tebl/NoiseMaker/documentation/datasheet/passive_buzzer.png

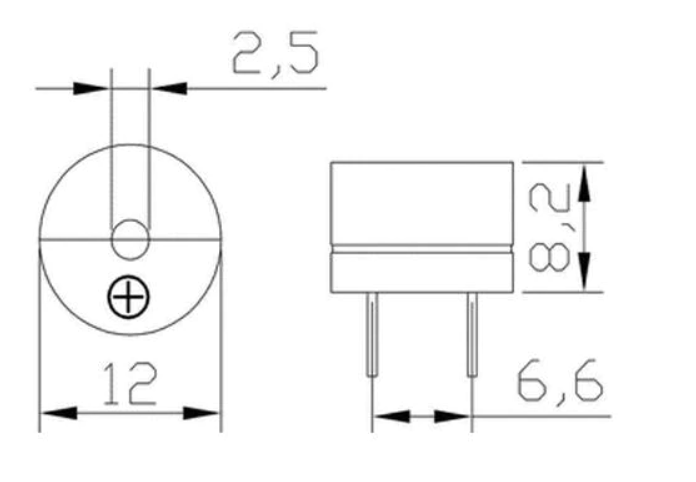
documentation/datasheet/passive_buzzer.png
