tebl/NoiseMaker/gallery/2022-11-01 22.10.24.jpg

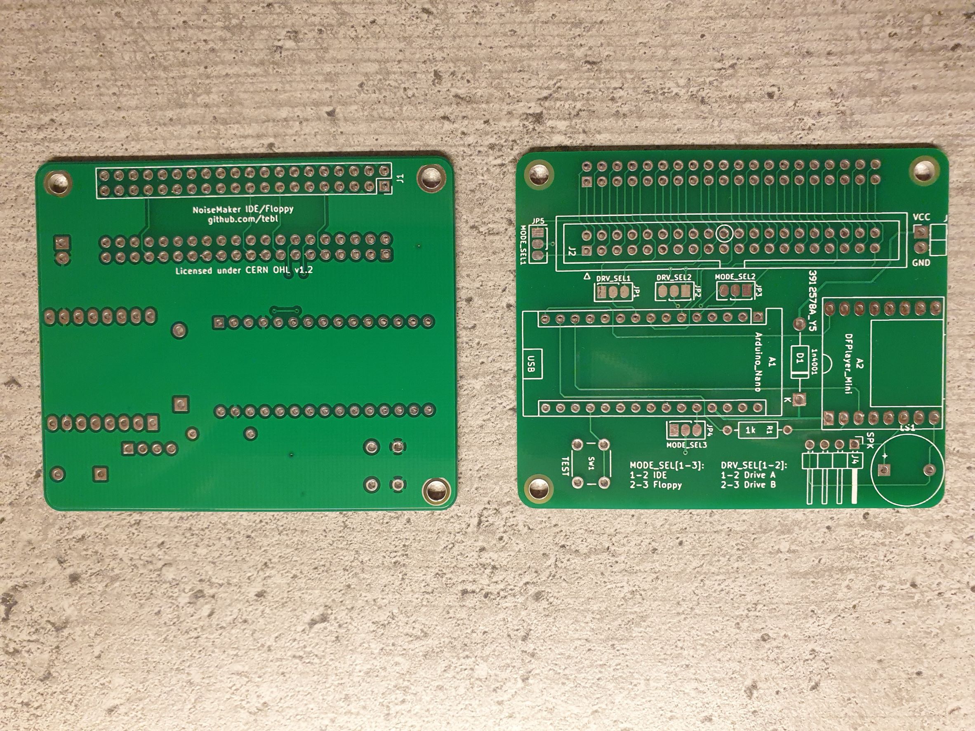
gallery/2022-11-01 22.10.24.jpg
