tebl/NoiseMaker/gallery/2022-11-27 00.52.01.jpg

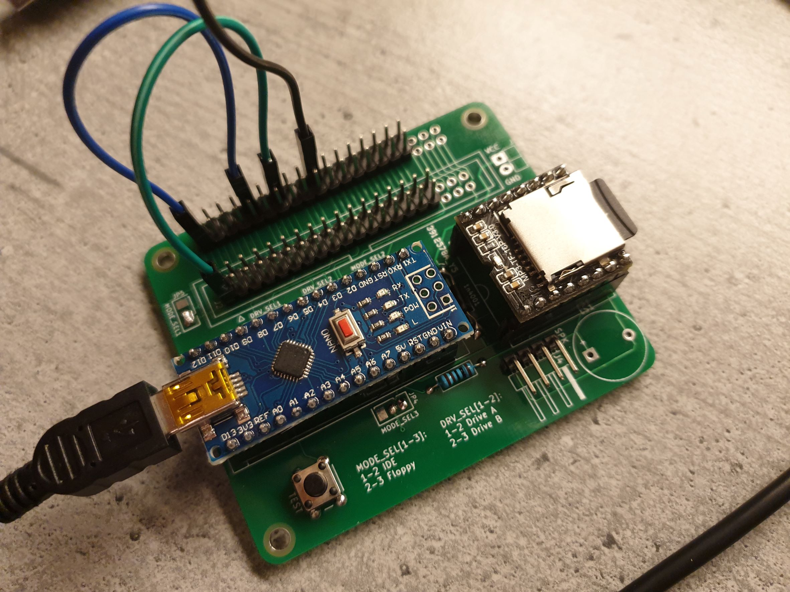
gallery/2022-11-27 00.52.01.jpg
