tebl/NoiseMaker/gallery/2023-01-08 01.55.44.jpg

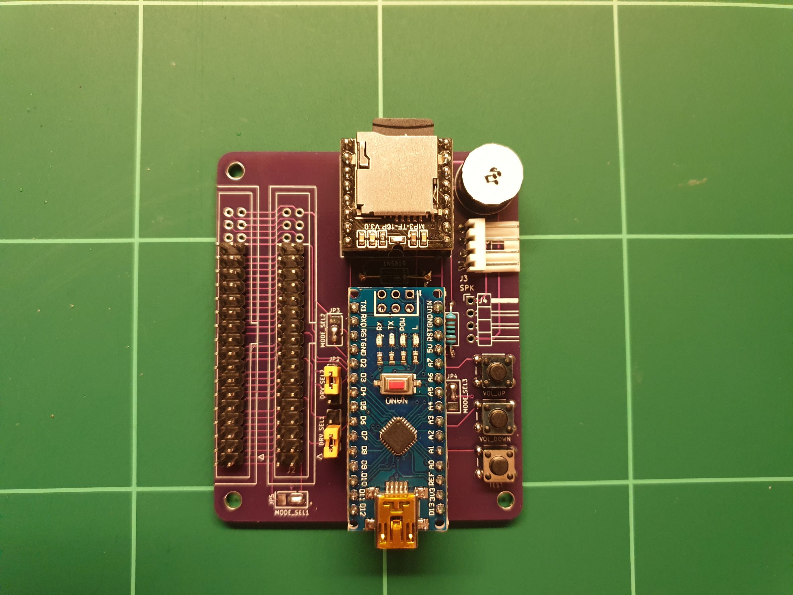
gallery/2023-01-08 01.55.44.jpg
