tebl/NoiseMaker/gallery/2023-01-09 14.08.43.jpg

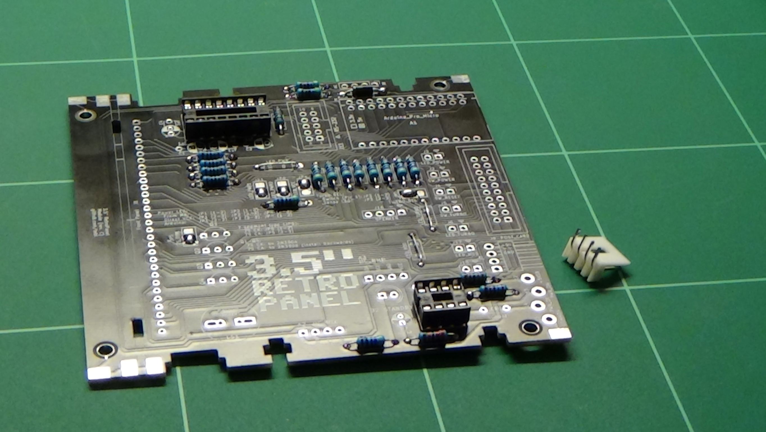
gallery/2023-01-09 14.08.43.jpg
