tebl/NoiseMaker/gallery/2023-01-14 02.07.19.jpg

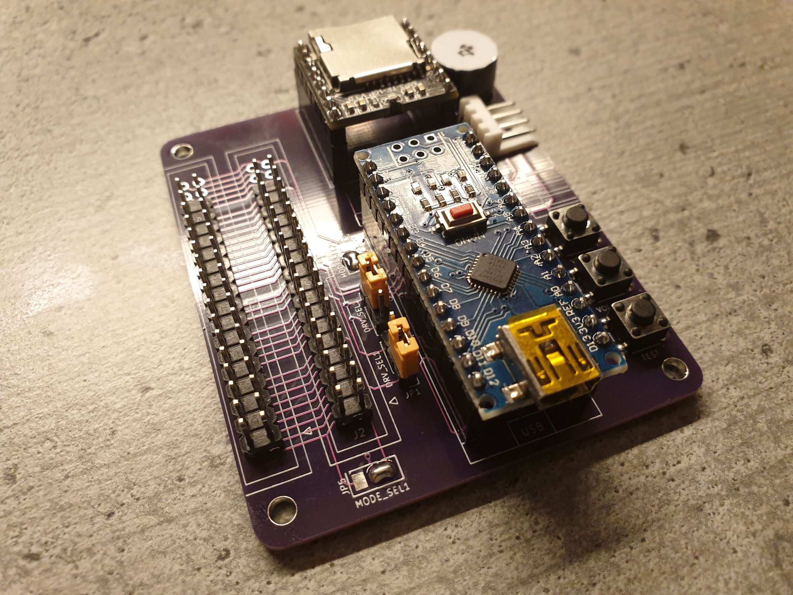
gallery/2023-01-14 02.07.19.jpg
