tebl/NoiseMaker/gallery/NoiseMaker.png

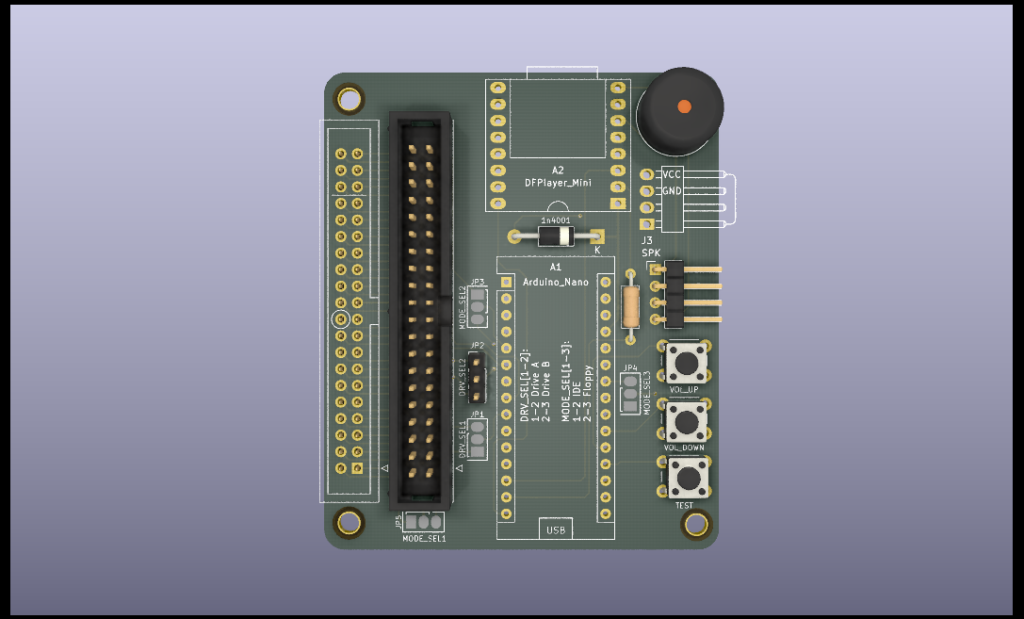
gallery/NoiseMaker.png
