tebl/NoiseMaker/software/arduino/NoiseMaker/NoiseMaker/commands.h

#include <Arduino.h>
void print_help();
void print_version();
void print_welcome();
void volume_up();
void volume_down();
void update_volume(int8_t value);
void update_profile(int8_t value);

bool handle_command(String command, String name, void (*function)());
void select_command(String command);
void echo_command(String command);
void echo_unknown(String command);
