tebl/NoiseMaker/software/arduino/NoiseMaker/NoiseMaker/debug.h

#pragma once
#include "settings.h"

#ifdef DEBUG
 #define DEBUG_PRINT(x)  Serial.print(x); 
#else
 #define DEBUG_PRINT(x)
#endif
#ifdef DEBUG
 #define DEBUG_PRINTLN(x)  Serial.println(x);
#else
 #define DEBUG_PRINTLN(x)
#endif
#ifdef DEBUG_VERBOSE
 #define DEBUG_SPINLOCK(x)  Serial.print(x); delay(1);
#else
 #define DEBUG_SPINLOCK(x)  delay(1);
#endif
